rogovogor17/PlayStationPortable/src/Map.cpp

#include "Map.hpp"

//////////////////////////////////////////////////
//Every map shall contain 3 rows in the end declared as BEDROCK

uint8_t map_level_1[MAP_HEIGHT][MAP_WIDTH] = {
    
    {1, 1, 1, 1, 1, 1, 1, 1, 1, 1, 1, 1, 1, 1, 1, 1, 1, 1, 1, 1, 3, 3, 3, 3},// Ряд 0
    {1, 0, 0, 0, 0, 0, 0, 0, 0, 0, 0, 0, 0, 0, 0, 0, 0, 0, 0, 0, 3, 3, 3, 3},// Ряд 1
    {1, 0, 2, 2, 0, 0, 2, 2, 2, 2, 2, 2, 2, 2, 2, 2, 2, 2, 0, 0, 3, 3, 3, 3},// Ряд 2
    {1, 0, 2, 2, 0, 0, 2, 0, 0, 0, 0, 0, 0, 0, 0, 0, 0, 2, 0, 0, 3, 3, 3, 3},// Ряд 3
    {1, 0, 2, 2, 0, 0, 2, 0, 1, 1, 0, 0, 5, 0, 1, 1, 0, 2, 0, 0, 3, 3, 3, 3},// Ряд 4
    {1, 0, 2, 2, 0, 0, 2, 0, 0, 0, 0, 0, 0, 0, 0, 0, 0, 2, 0, 0, 3, 3, 3, 3},// Ряд 5
    {1, 0, 2, 2, 0, 0, 2, 2, 2, 2, 2, 2, 2, 2, 2, 2, 2, 2, 0, 0, 3, 3, 3, 3},// Ряд 6
    {1, 0, 0, 0, 0, 0, 0, 0, 0, 0, 0, 0, 0, 0, 0, 0, 0, 0, 0, 0, 3, 3, 3, 3},// Ряд 7
    {1, 0, 0, 2, 2, 2, 0, 2, 2, 2, 0, 0, 0, 2, 2, 2, 0, 2, 2, 2, 3, 3, 3, 3},// Ряд 8
    {1, 0, 0, 0, 0, 2, 0, 2, 0, 2, 0, 0, 0, 0, 0, 2, 0, 2, 0, 0, 3, 3, 3, 3},// Ряд 9
    {1, 0, 0, 2, 2, 2, 0, 2, 0, 2, 0, 0, 0, 2, 2, 2, 0, 2, 2, 2, 3, 3, 3, 3},// Ряд 10
    {1, 0, 0, 2, 0, 0, 0, 2, 0, 2, 0, 0, 0, 2, 0, 0, 0, 2, 0, 2, 3, 3, 3, 3},// Ряд 11
    {1, 0, 0, 2, 0, 0, 0, 2, 0, 2, 0, 0, 0, 2, 0, 0, 0, 2, 0, 2, 3, 3, 3, 3},// Ряд 12
    {1, 0, 0, 2, 2, 2, 0, 2, 2, 2, 1, 1, 1, 2, 2, 2, 0, 2, 2, 2, 3, 3, 3, 3},// Ряд 13
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
};

struct Level attributes_level_3 = {
    .map = map_level_3,
    .spawn_place_p1 = {0, 0},
    .amount_of_bots_to_spawn = 10,
    .bot_spawns = {},
    .time_between_spawns_tick = 50,
};

Level levels[] = {attributes_level_1, attributes_level_2, attributes_level_3};
